VISWAJITH1997/Gesture-Recognition-Using-Machine-Learning/Desgin Sketch/Sample 4/signLan_etch_paste_mask_top_mirror.pdf

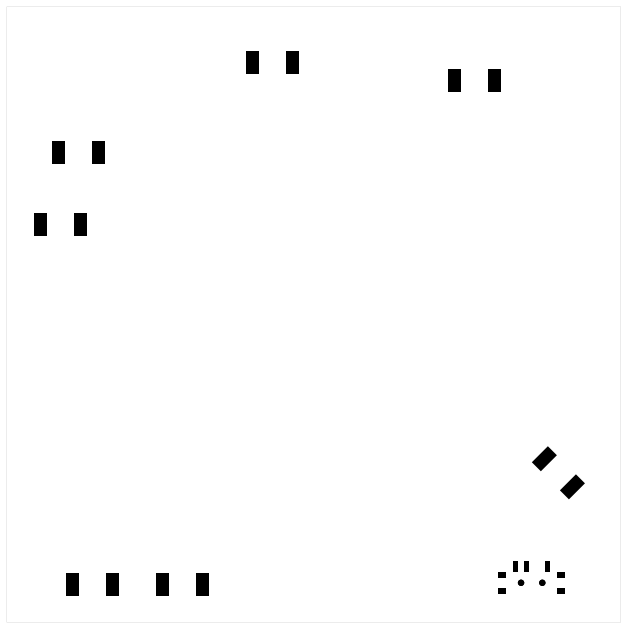
[picture p26: figure]
