VISWAJITH1997/Gesture-Recognition-Using-Machine-Learning/Screenshots/cmd sprint.png

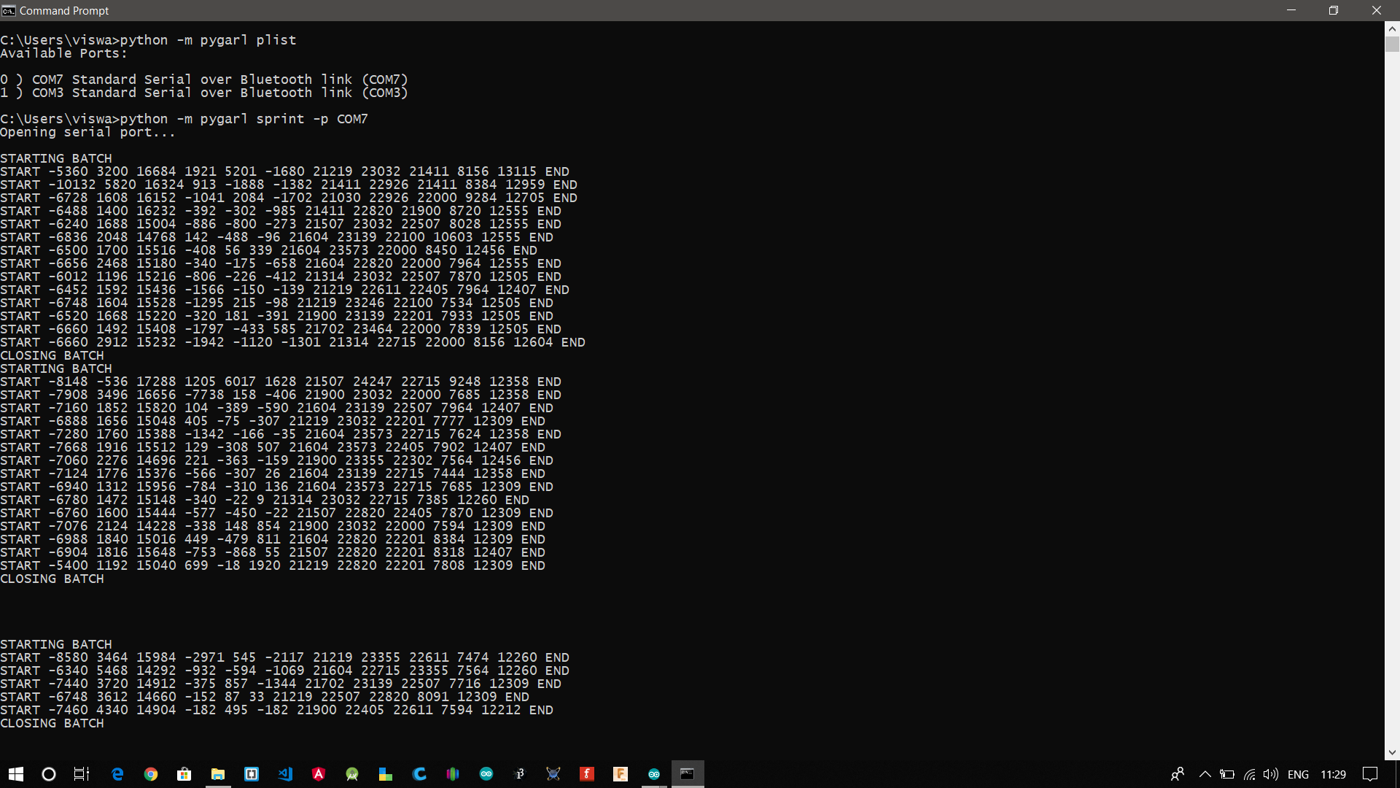
Screenshots/cmd sprint.png
