VISWAJITH1997/Gesture-Recognition-Using-Machine-Learning/Screenshots/Android Serial Print.jpg

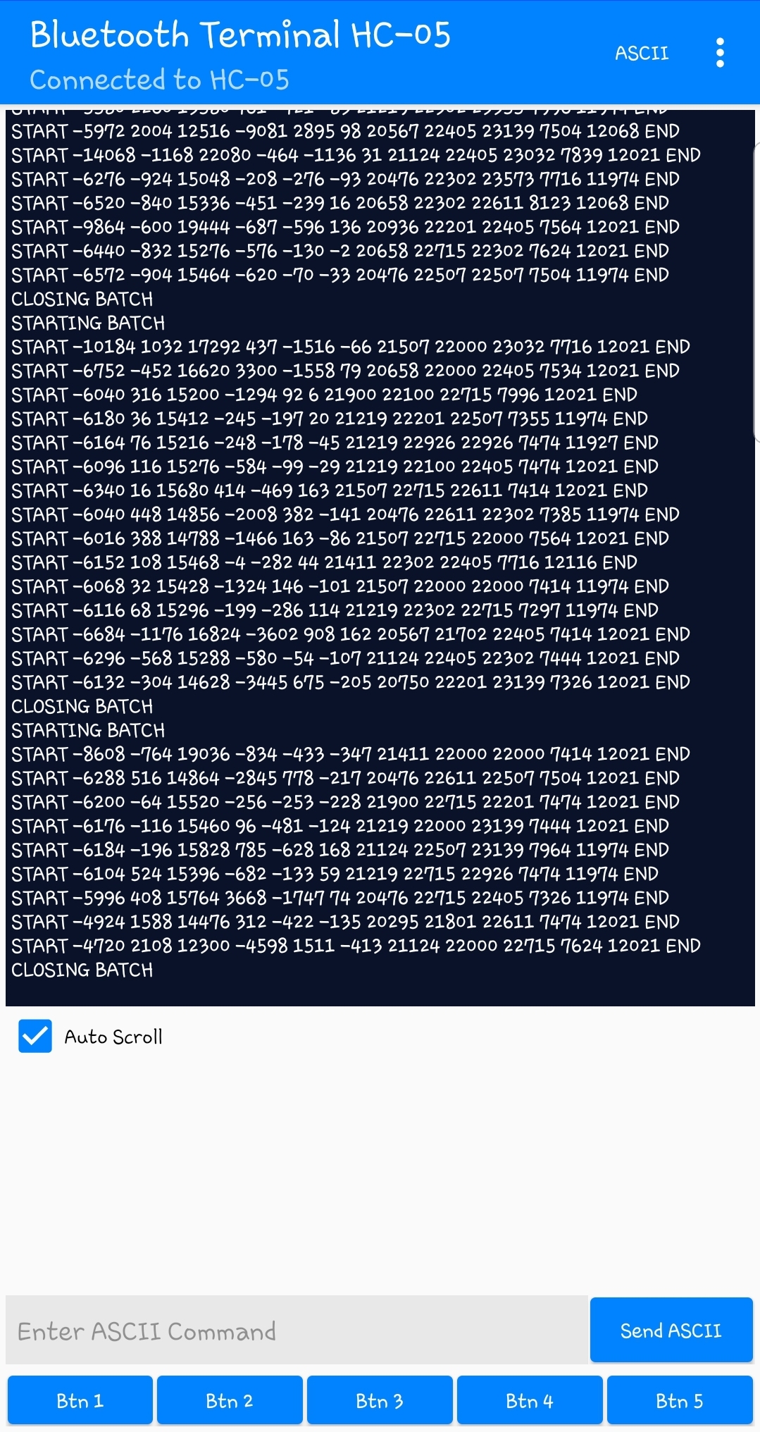
Screenshots/Android Serial Print.jpg
