VISWAJITH1997/Gesture-Recognition-Using-Machine-Learning/Codes/Connections/Untitled Sketch_etch_silk_bottom.pdf

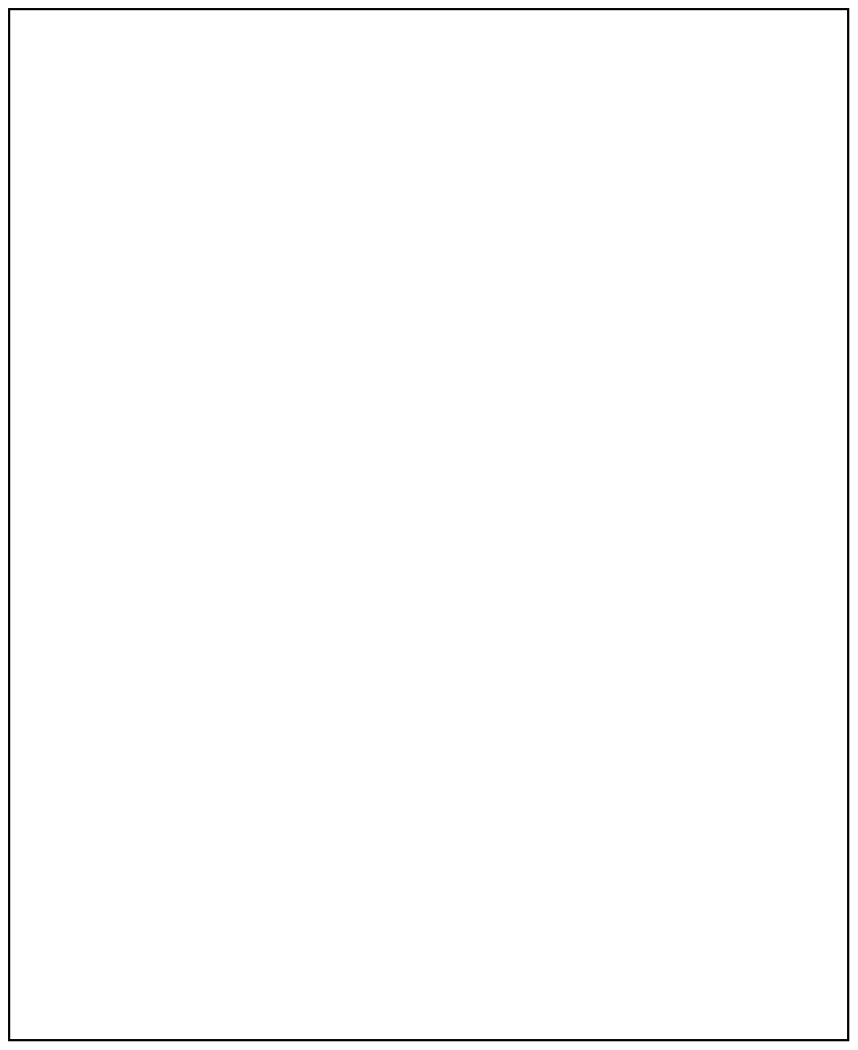
[picture p43: page 1]
