VISWAJITH1997/Gesture-Recognition-Using-Machine-Learning/Codes/Connections/Untitled Sketch_etch_silk_bottom_mirror.pdf

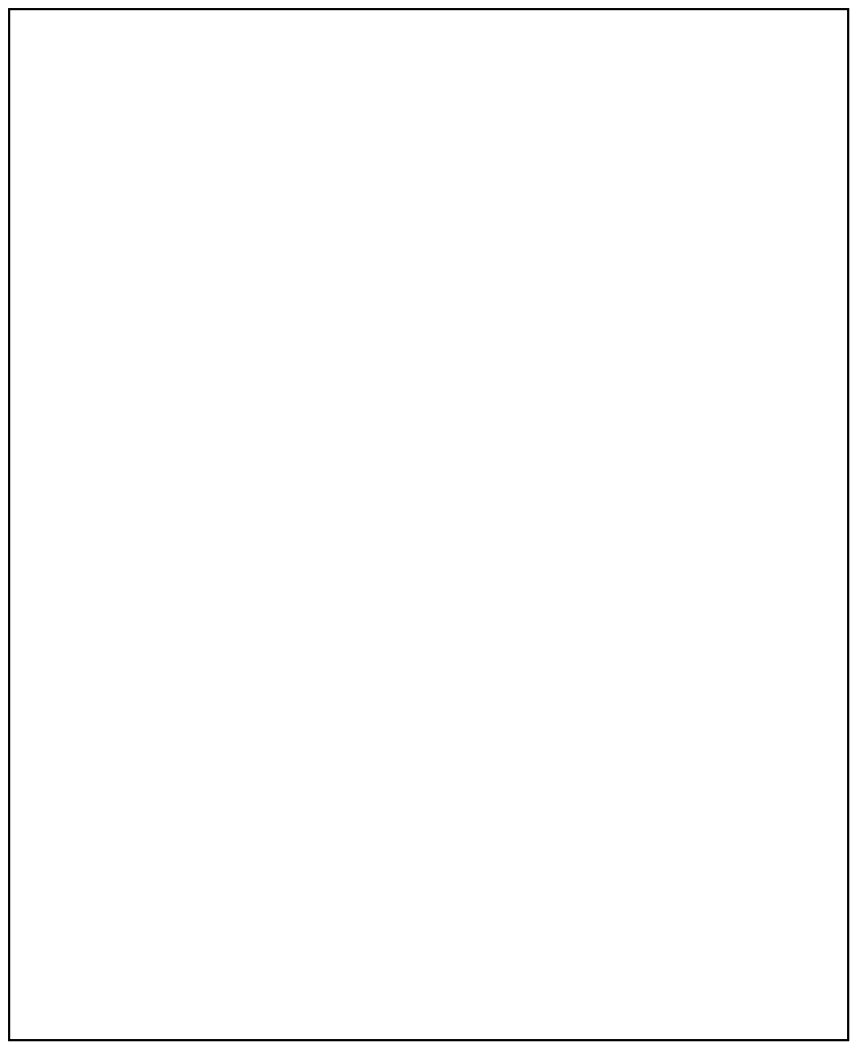
[picture p44: page 1]
