VISWAJITH1997/Gesture-Recognition-Using-Machine-Learning/Codes/Connections/Untitled Sketch_etch_silk_top.pdf

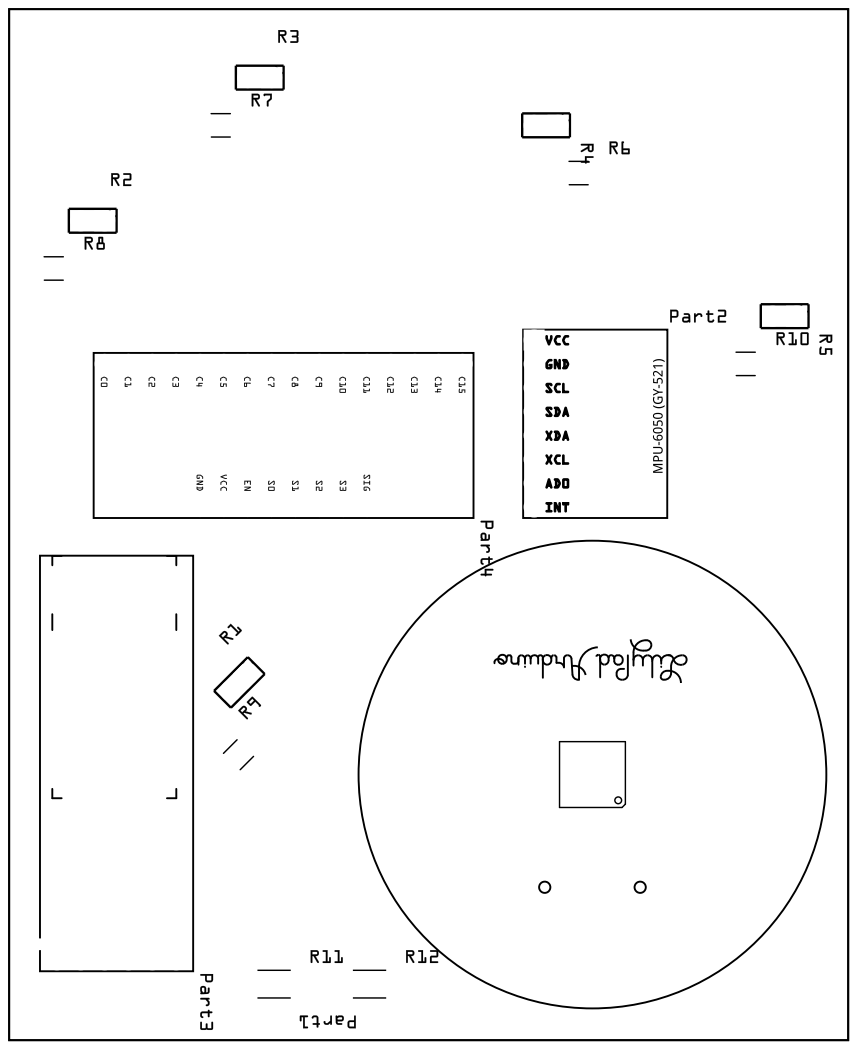
[picture p45: page 1]
