VISWAJITH1997/Gesture-Recognition-Using-Machine-Learning/Codes/Connections/Untitled Sketch_etch_silk_top_mirror.pdf

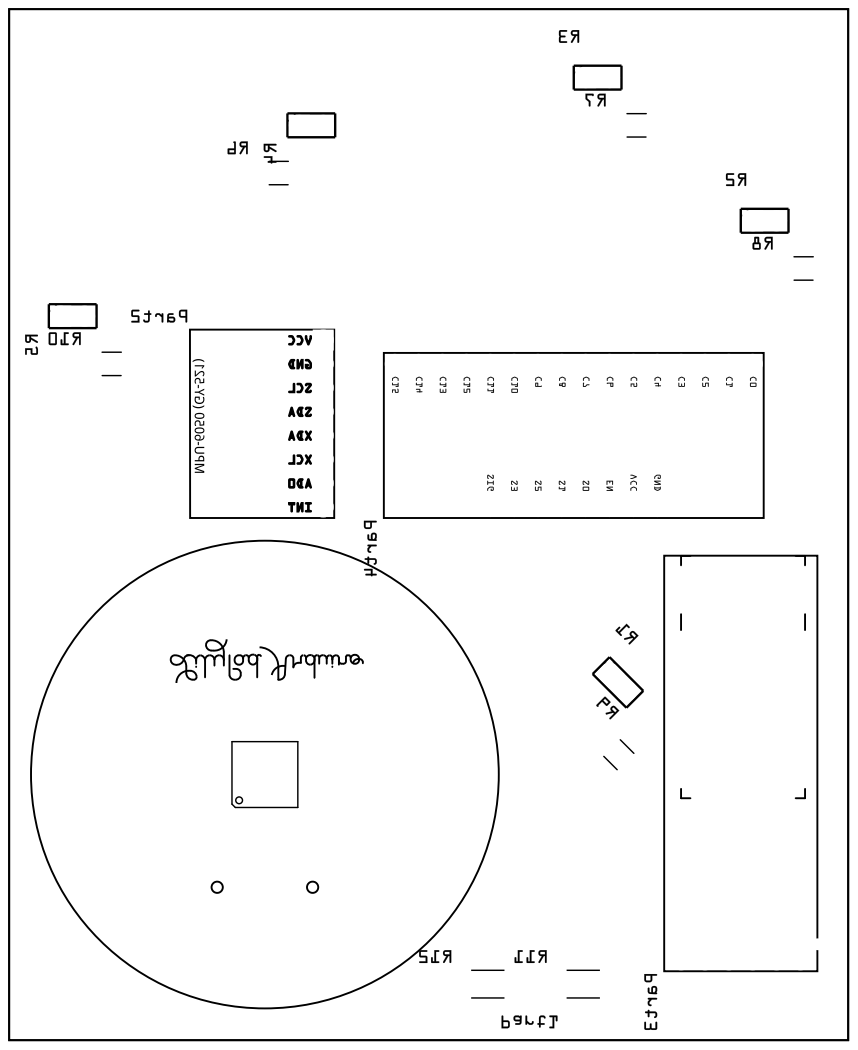
[picture p46: page 1]
