VISWAJITH1997/Gesture-Recognition-Using-Machine-Learning/Desgin Sketch/Sample 2/SignLanguage_etch_copper_bottom.pdf

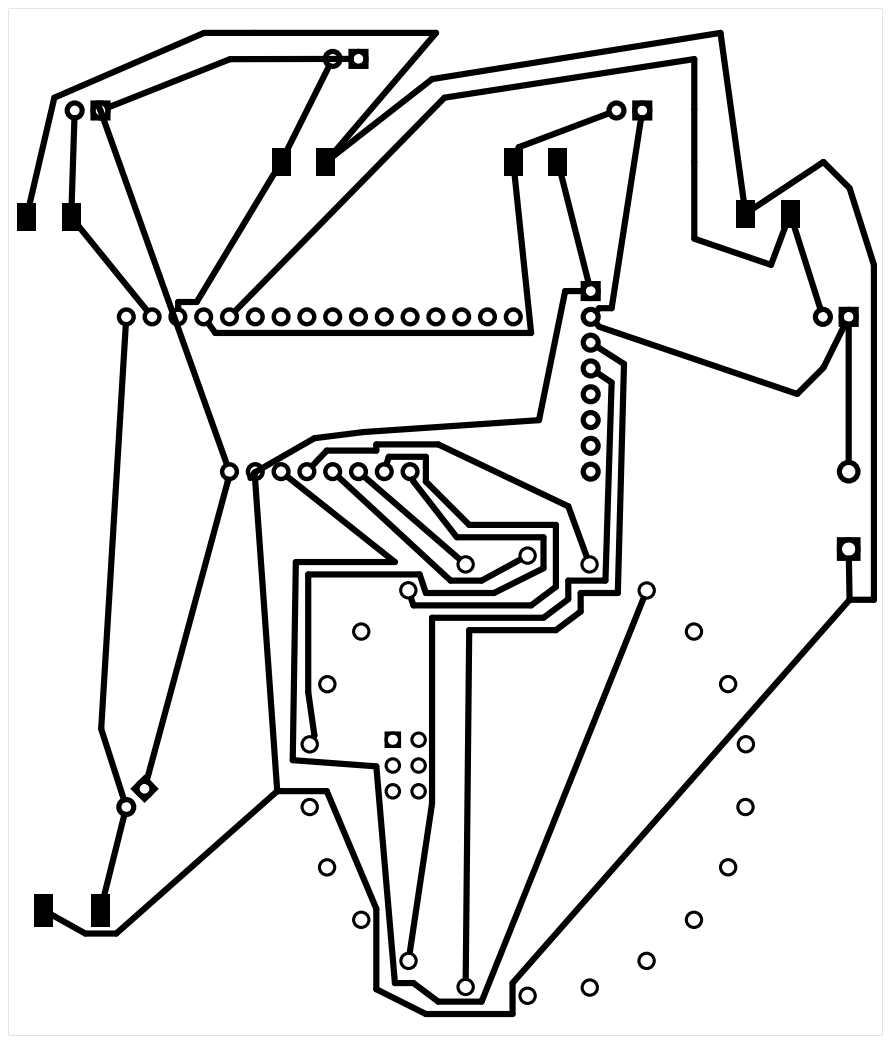
[picture p47: page 1]
