VISWAJITH1997/Gesture-Recognition-Using-Machine-Learning/Desgin Sketch/Sample 2/SignLanguage_etch_copper_bottom_mirror.pdf

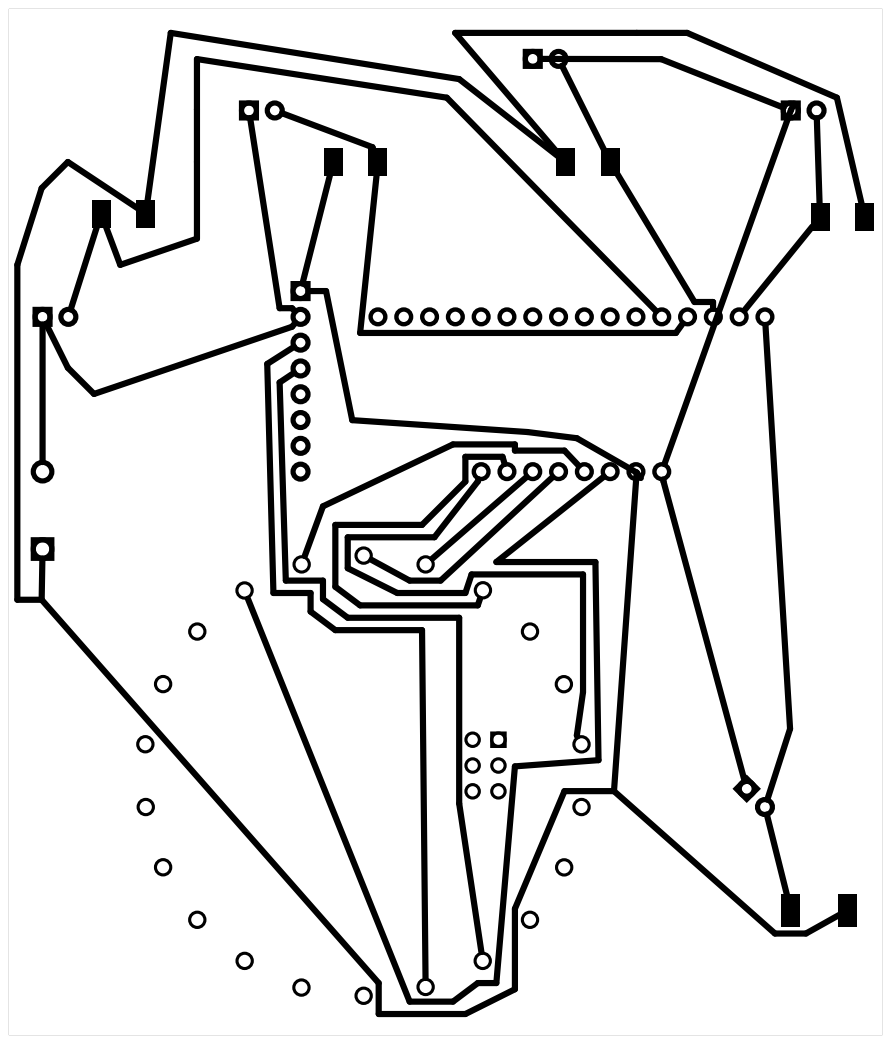
[picture p48: page 1]
