VISWAJITH1997/Gesture-Recognition-Using-Machine-Learning/Desgin Sketch/Sample 2/SignLanguage_etch_copper_top.pdf

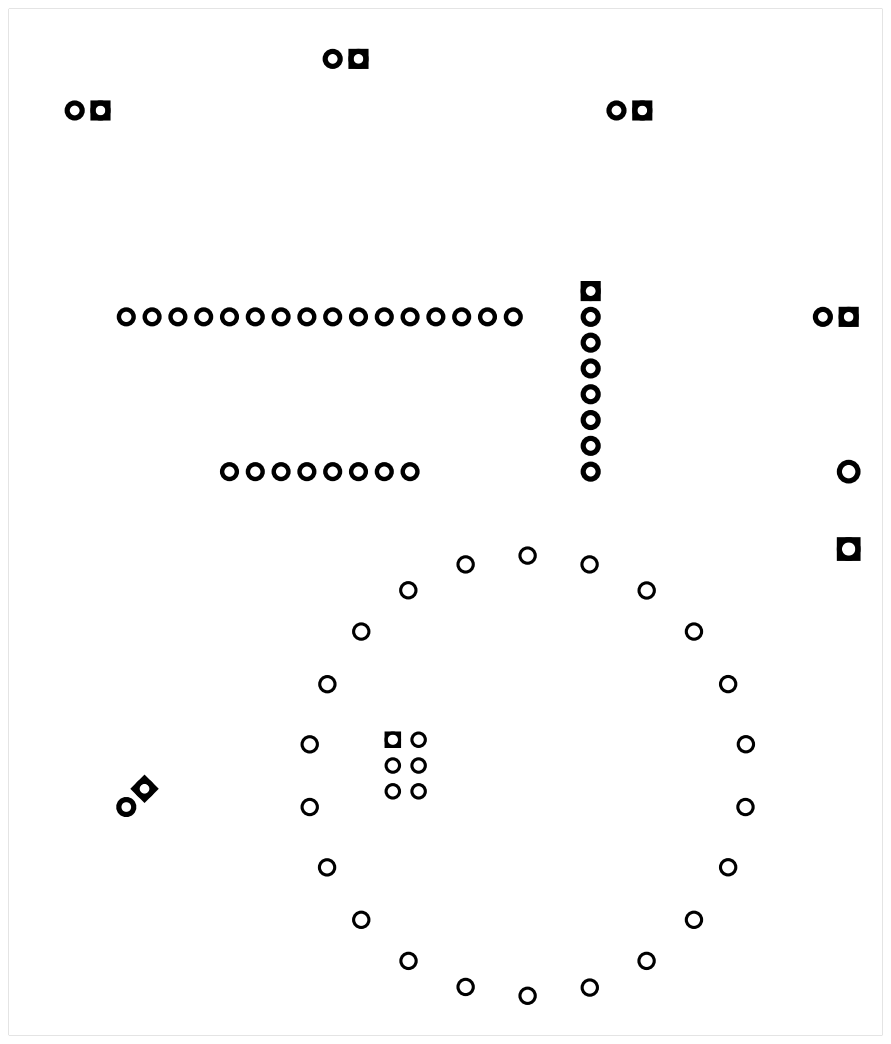
[picture p49: page 1]
