VISWAJITH1997/Gesture-Recognition-Using-Machine-Learning/Desgin Sketch/Sample 2/SignLanguage_etch_copper_top_mirror.pdf

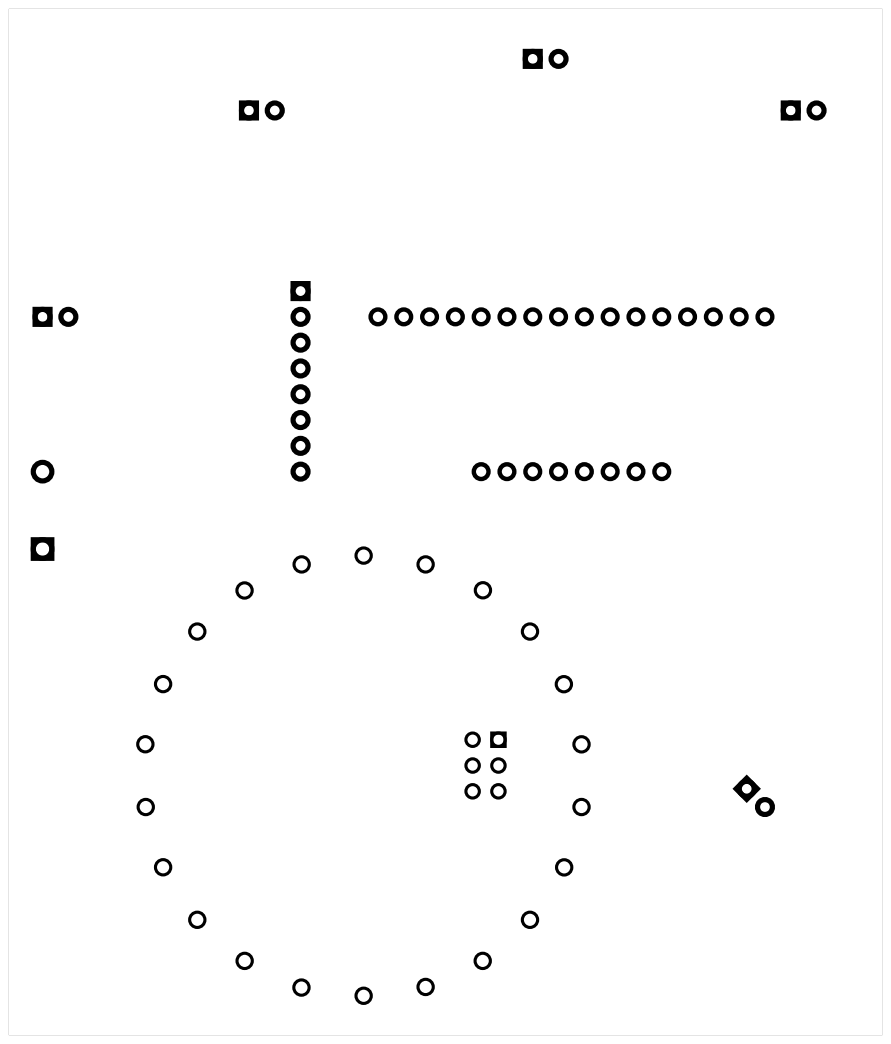
[picture p50: page 1]
