VISWAJITH1997/Gesture-Recognition-Using-Machine-Learning/Desgin Sketch/Sample 2/SignLanguage_etch_mask_bottom.pdf

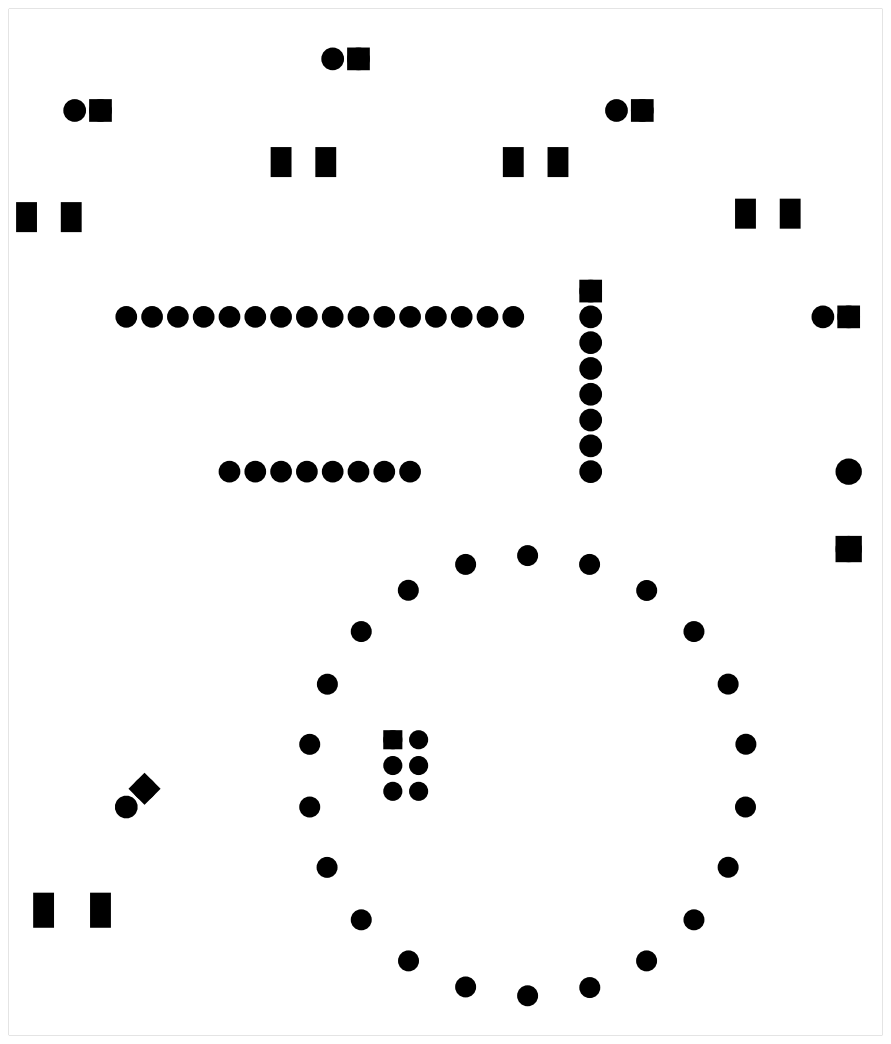
[picture p51: page 1]
