VISWAJITH1997/Gesture-Recognition-Using-Machine-Learning/Desgin Sketch/Sample 2/SignLanguage_etch_mask_bottom_mirror.pdf

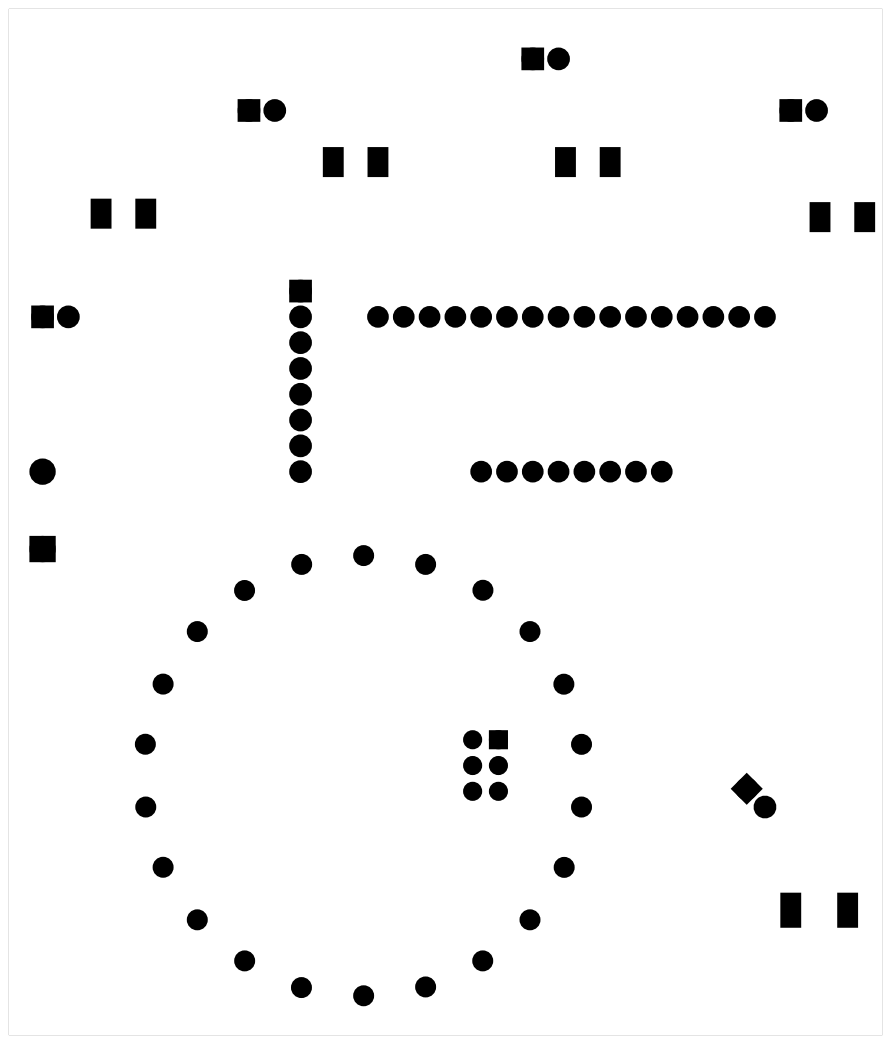
[picture p52: page 1]
