VISWAJITH1997/Gesture-Recognition-Using-Machine-Learning/Desgin Sketch/Sample 2/SignLanguage_etch_mask_top_mirror.pdf

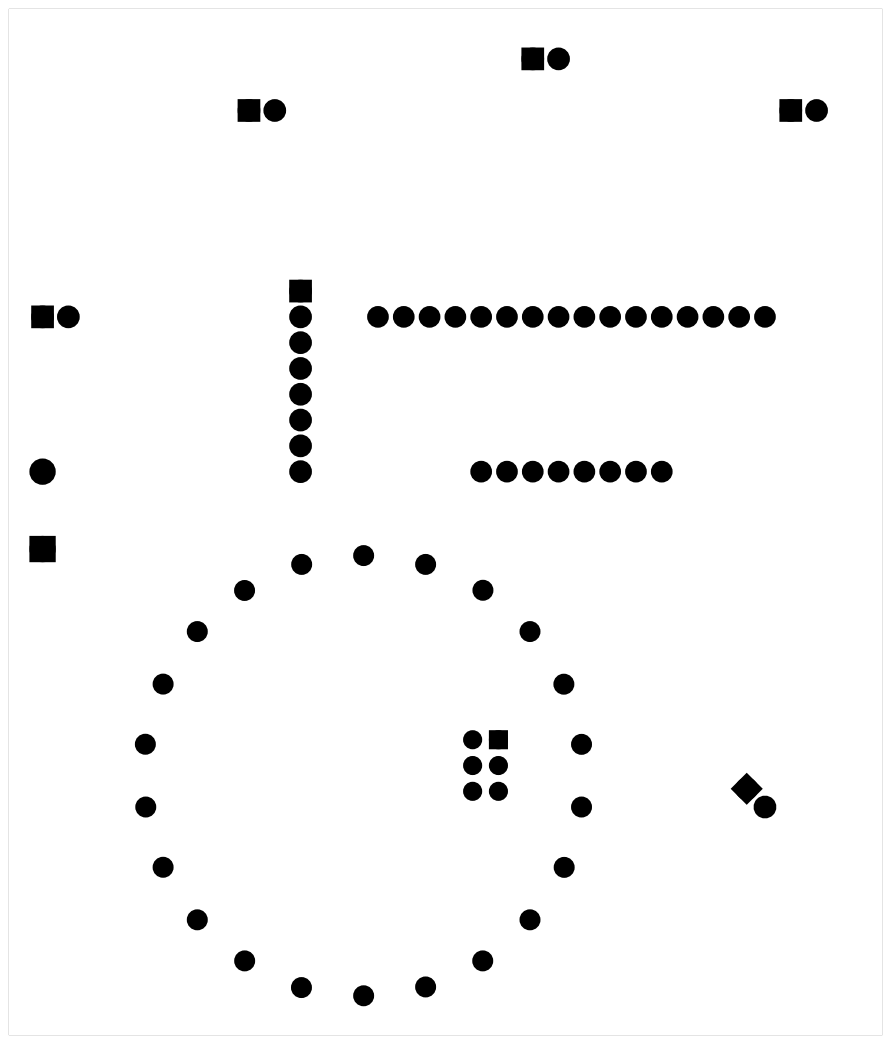
[picture p54: page 1]
