VISWAJITH1997/Gesture-Recognition-Using-Machine-Learning/Desgin Sketch/Sample 2/SignLanguage_etch_silk_bottom_mirror.pdf

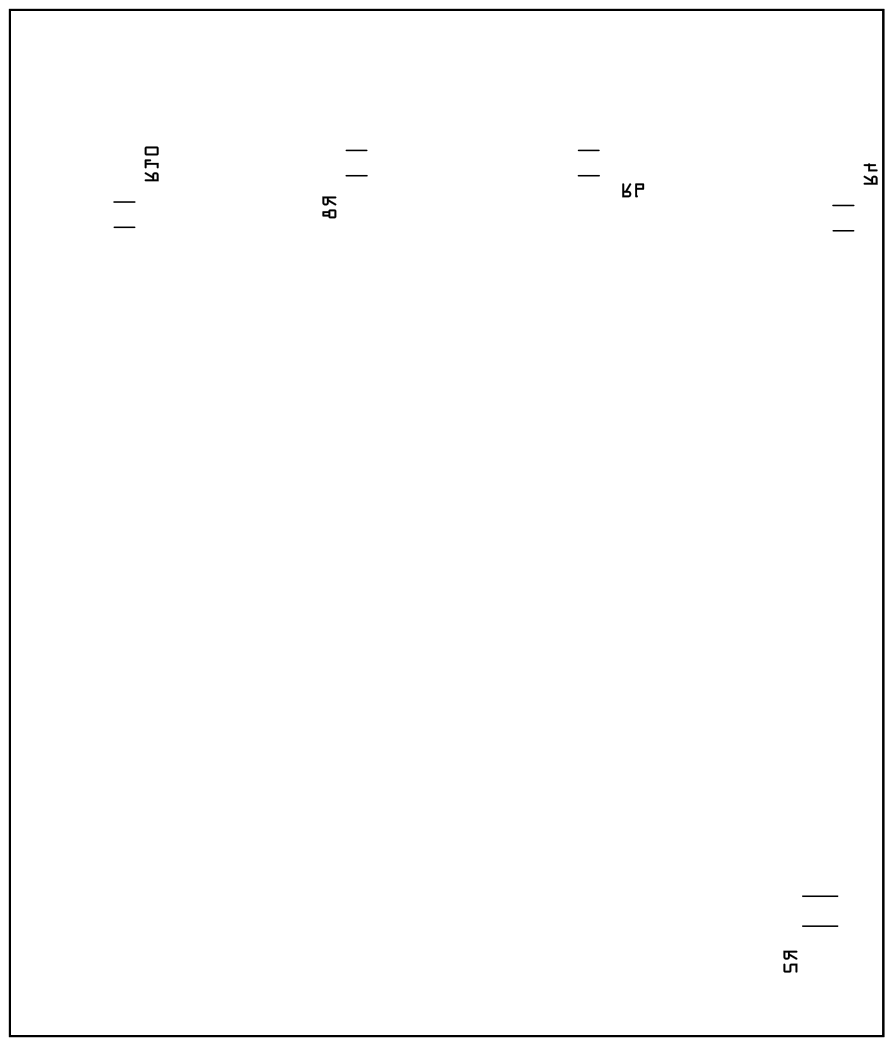
[picture p56: page 1]
