VISWAJITH1997/Gesture-Recognition-Using-Machine-Learning/Desgin Sketch/Sample 2/SignLanguage_etch_silk_top_mirror.pdf

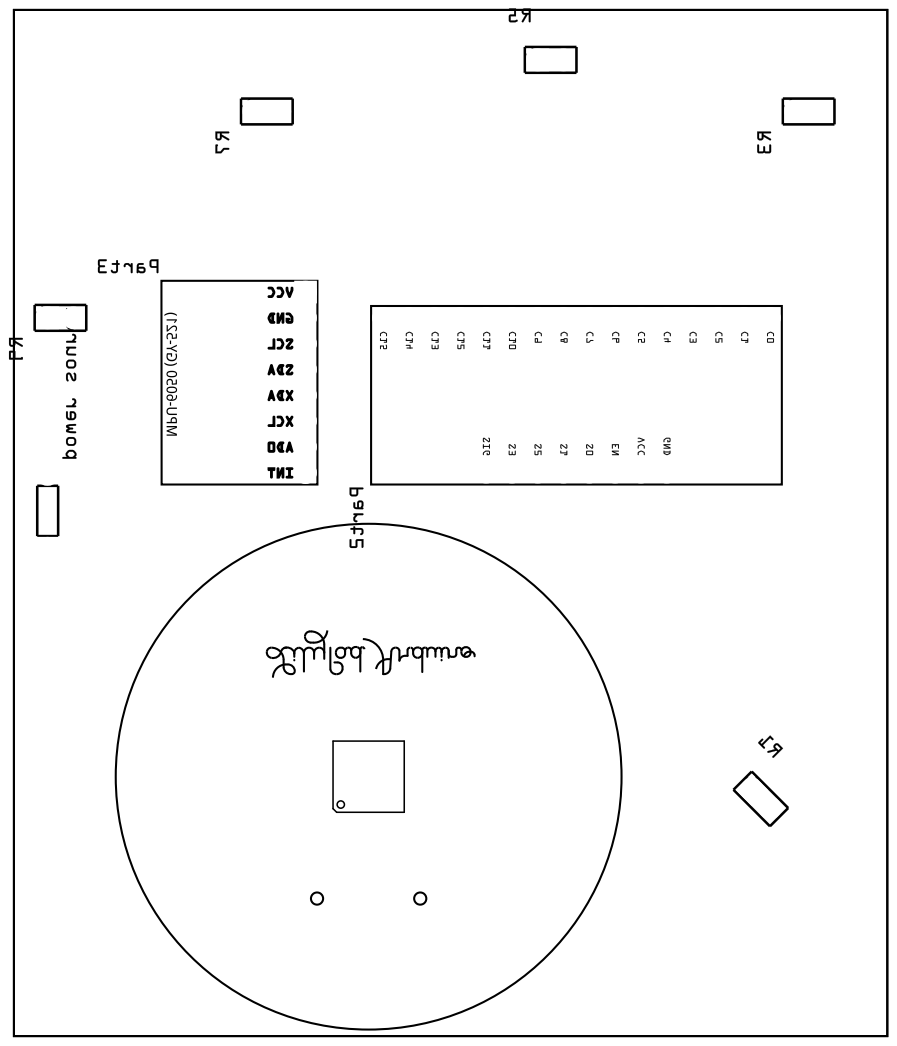
[picture p58: page 1]
