VISWAJITH1997/Gesture-Recognition-Using-Machine-Learning/Desgin Sketch/Sample 3/SignLanguage_etch_copper_bottom.pdf

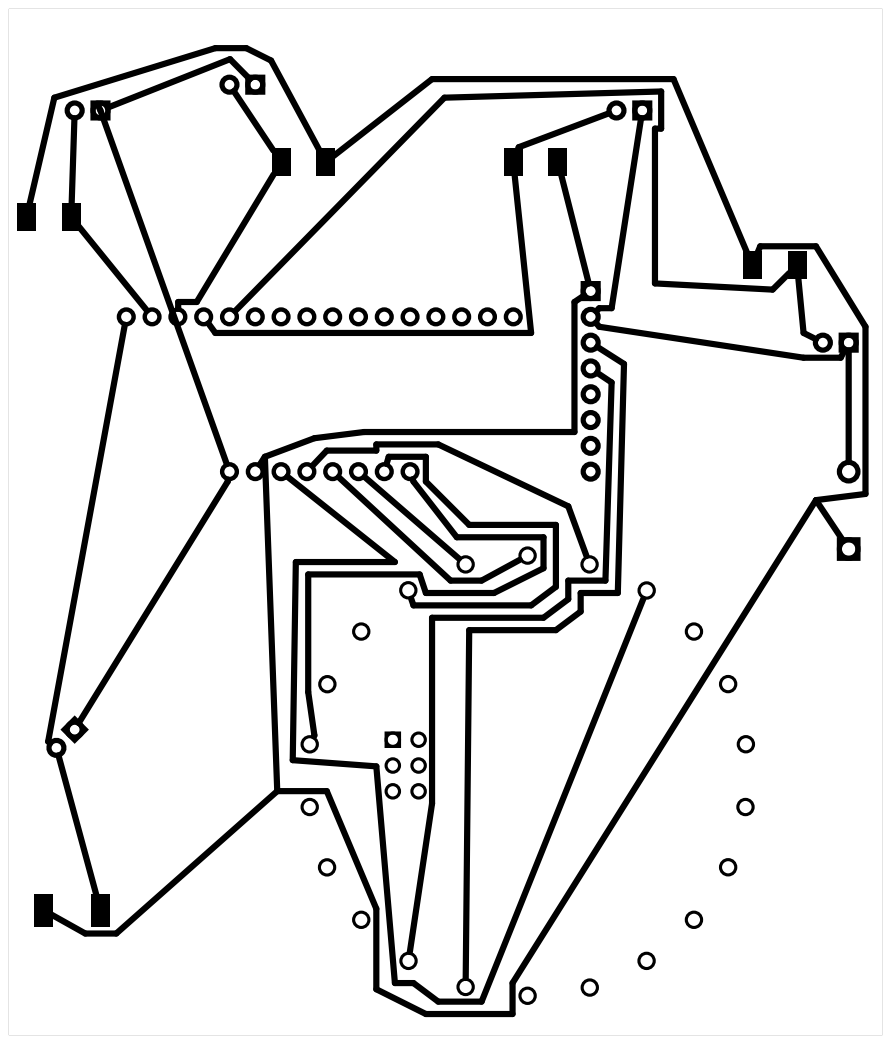
[picture p59: page 1]
