VISWAJITH1997/Gesture-Recognition-Using-Machine-Learning/Desgin Sketch/Sample 3/SignLanguage_etch_copper_bottom_mirror.pdf

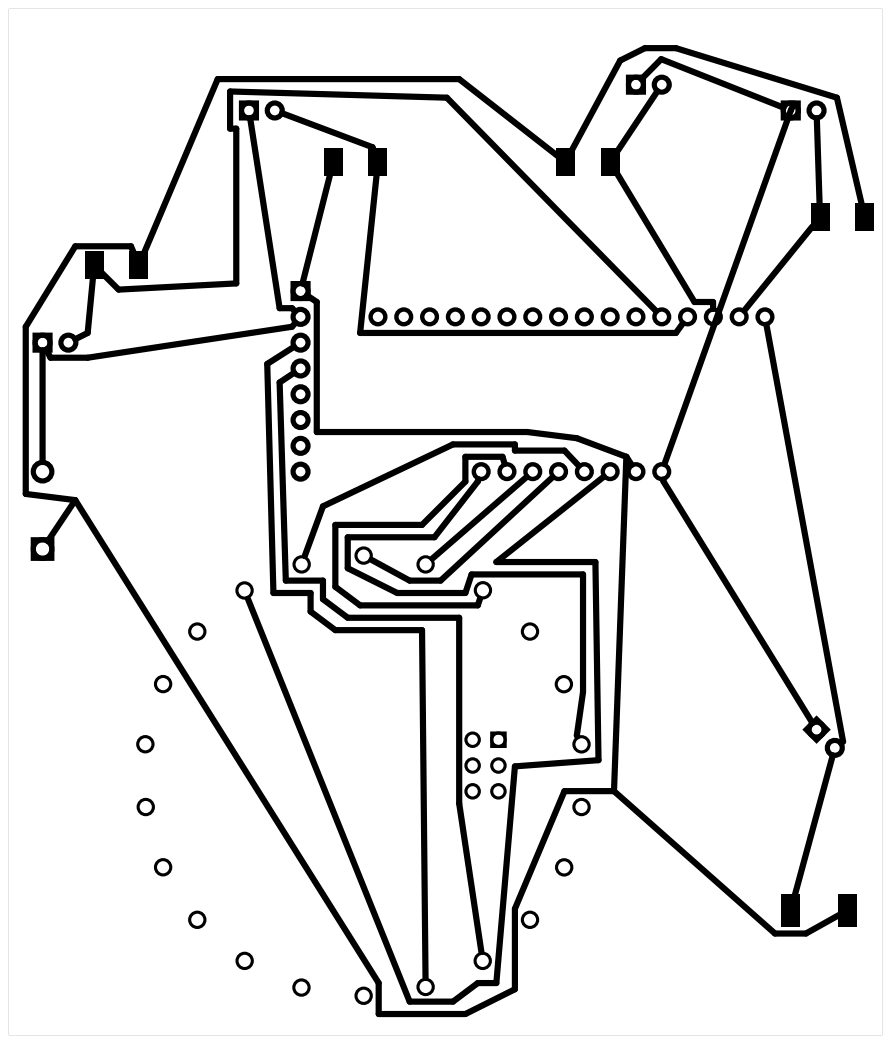
[picture p60: page 1]
