VISWAJITH1997/Gesture-Recognition-Using-Machine-Learning/Desgin Sketch/Sample 3/SignLanguage_etch_mask_bottom.pdf

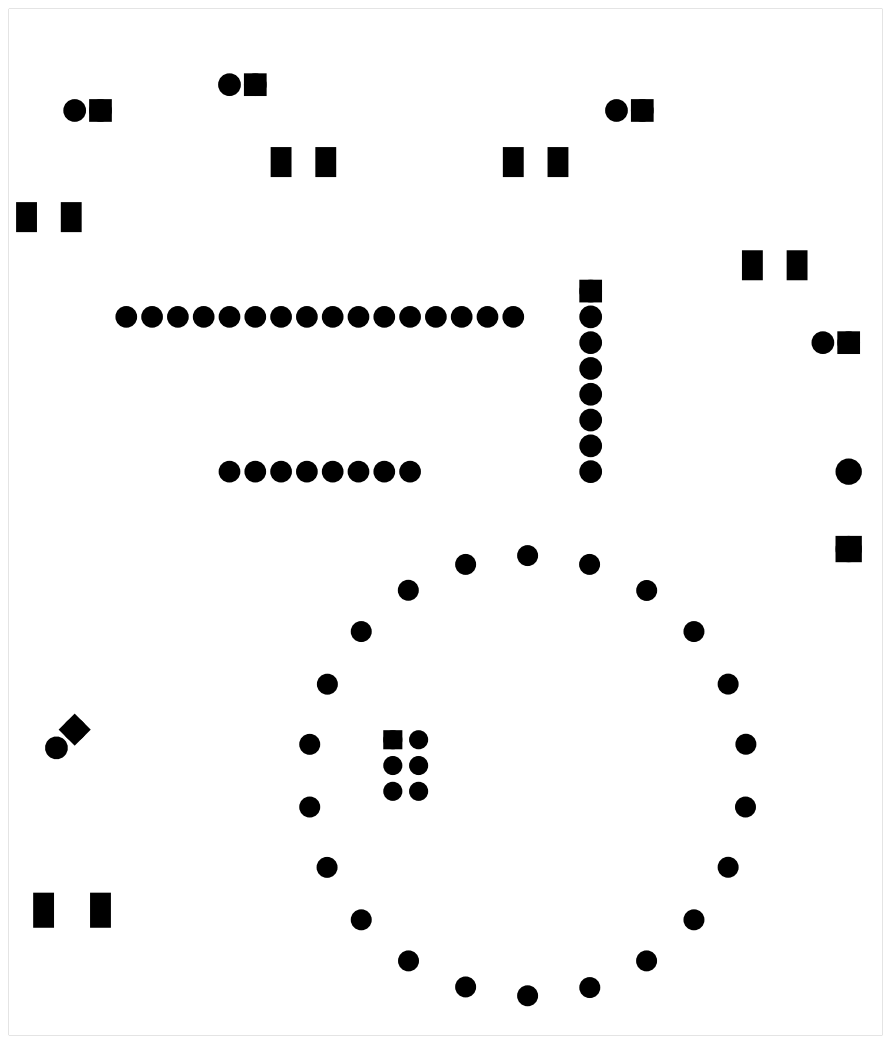
[picture p61: page 1]
