VISWAJITH1997/Gesture-Recognition-Using-Machine-Learning/Desgin Sketch/Sample 3/SignLanguage_etch_mask_bottom_mirror.pdf

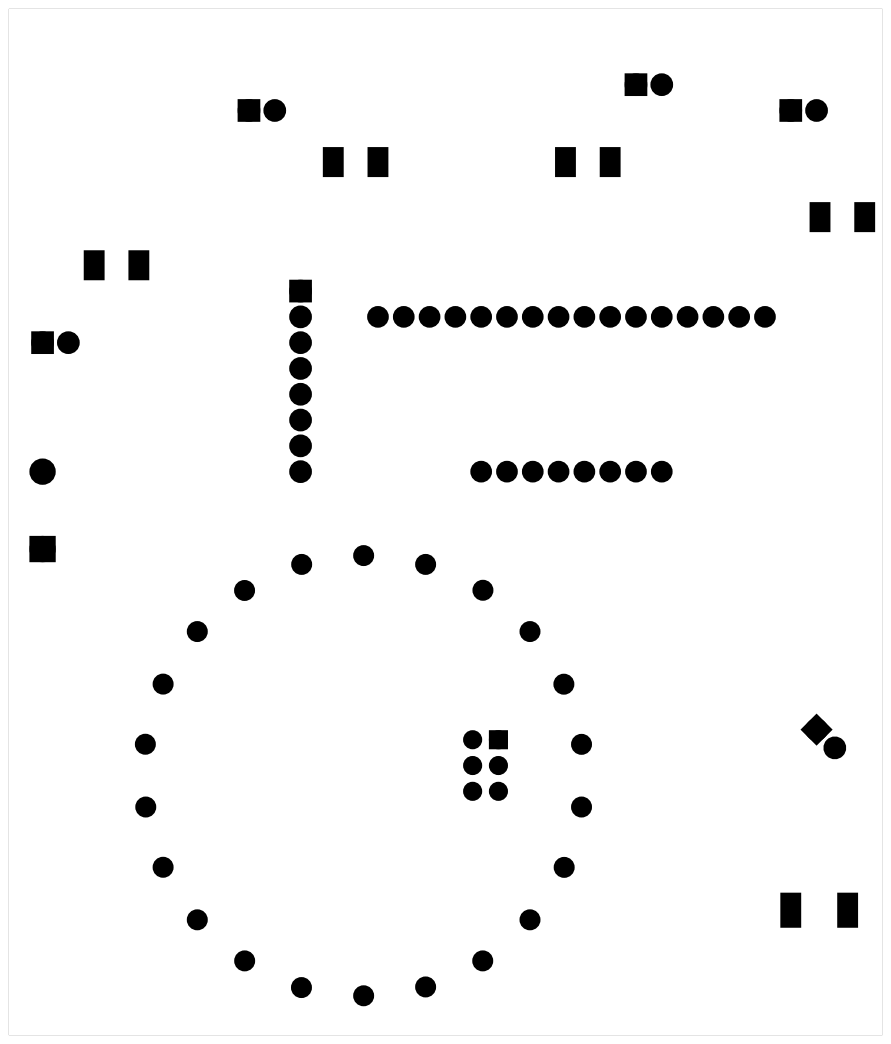
[picture p62: page 1]
