VISWAJITH1997/Gesture-Recognition-Using-Machine-Learning/Desgin Sketch/Sample 3/SignLanguage_etch_silk_bottom.pdf

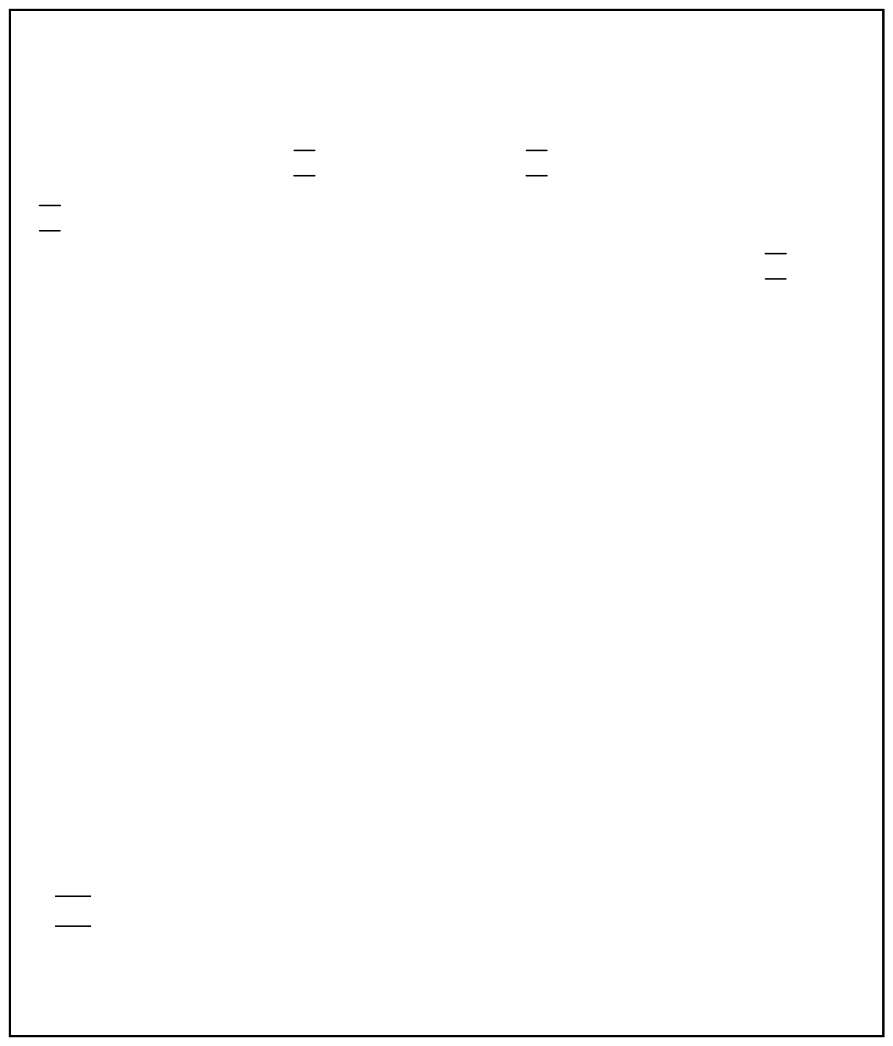
[picture p63: page 1]
