VISWAJITH1997/Gesture-Recognition-Using-Machine-Learning/Desgin Sketch/Sample 3/SignLanguage_etch_silk_bottom_mirror.pdf

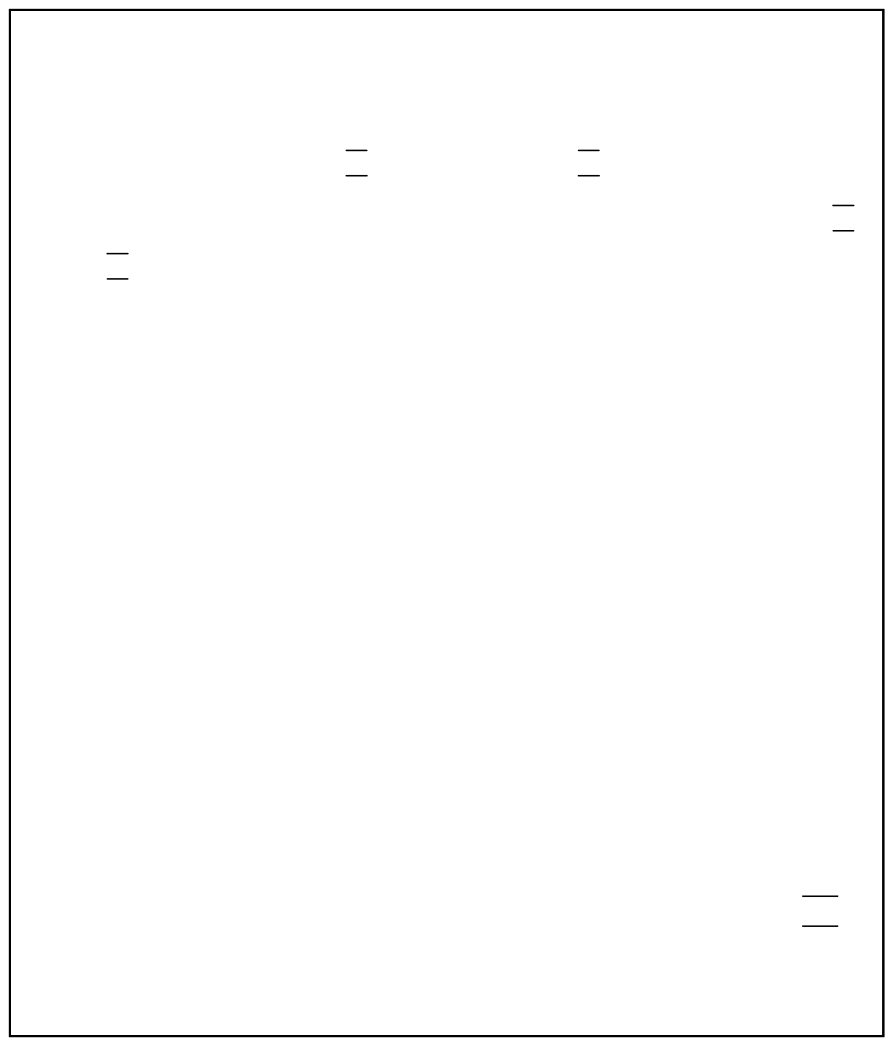
[picture p64: page 1]
