VISWAJITH1997/Gesture-Recognition-Using-Machine-Learning/Desgin Sketch/Sample 4/signLan_etch_copper_bottom.pdf

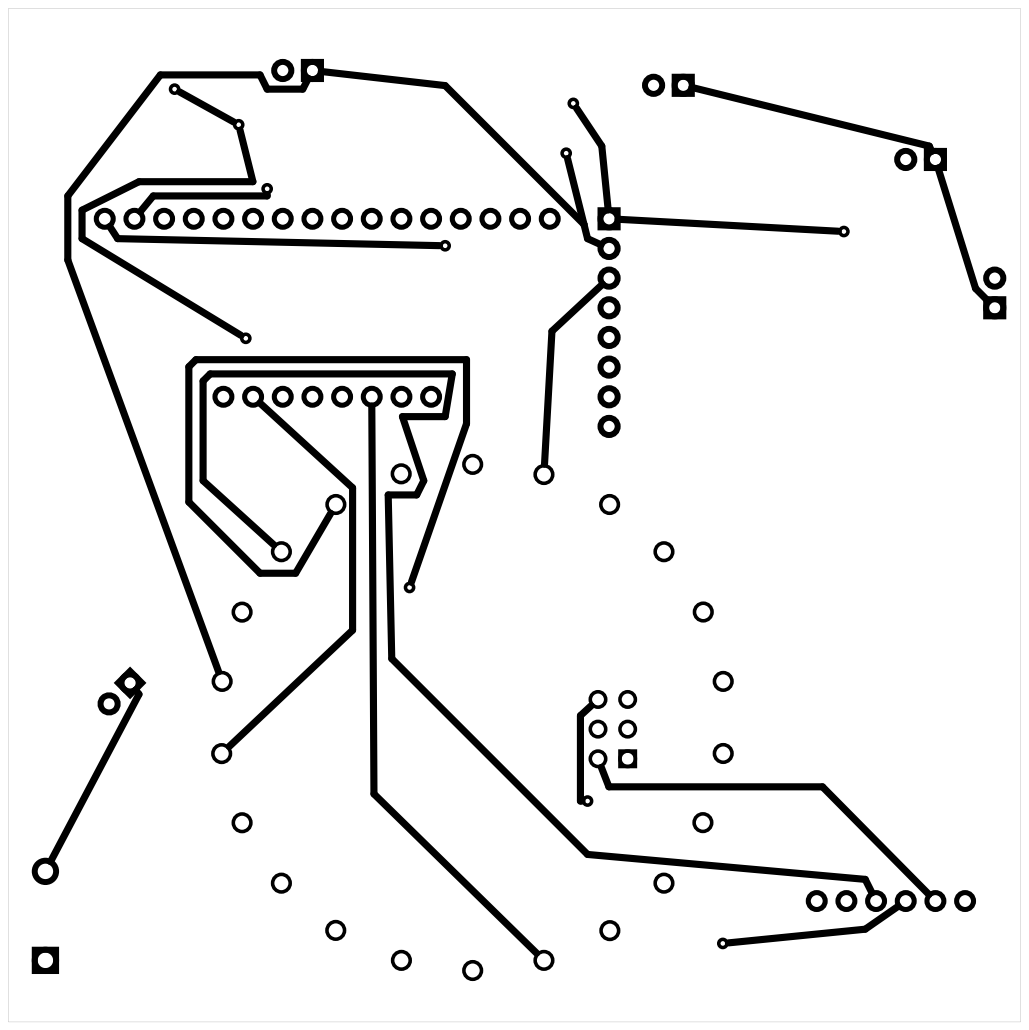
[picture p65: page 1]
