VISWAJITH1997/Gesture-Recognition-Using-Machine-Learning/Desgin Sketch/Sample 4/signLan_etch_copper_bottom_mirror.pdf

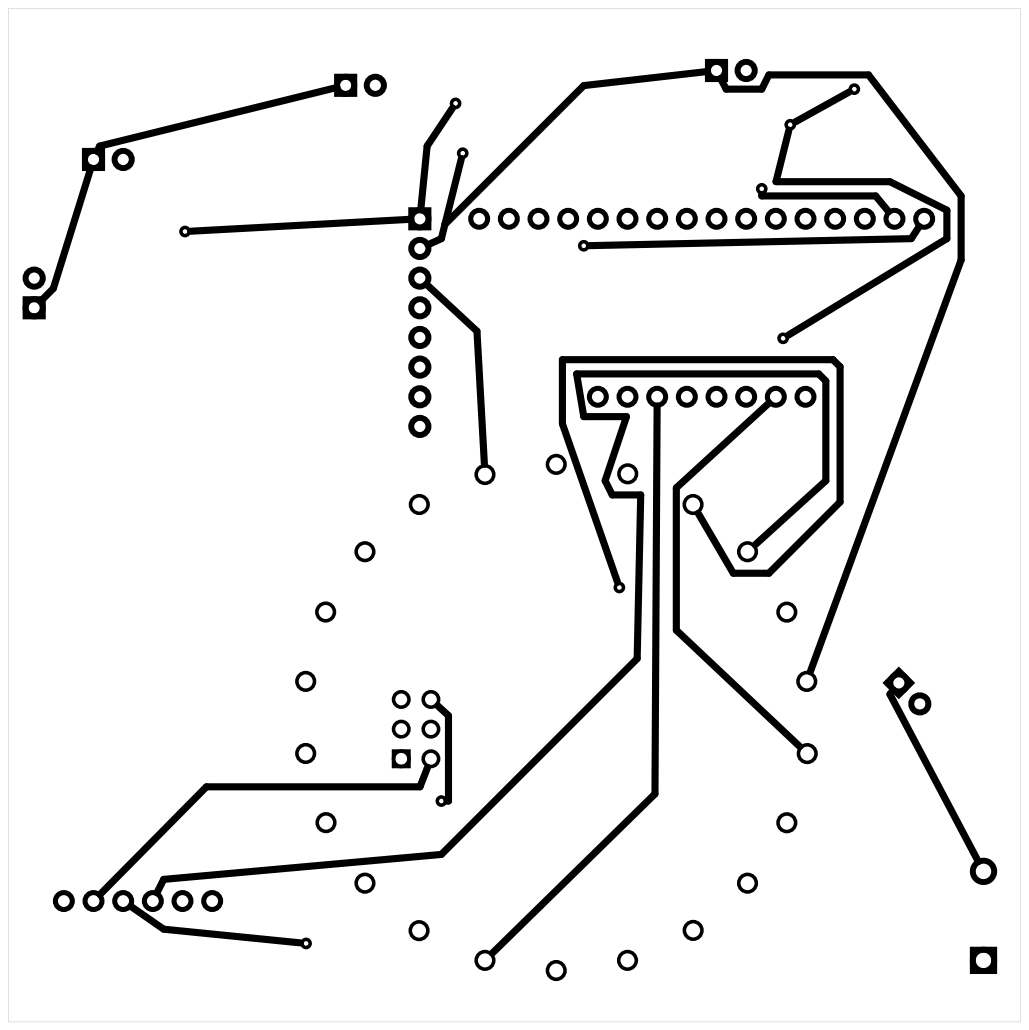
[picture p66: page 1]
