VISWAJITH1997/Gesture-Recognition-Using-Machine-Learning/Desgin Sketch/Sample 4/signLan_etch_copper_top.pdf

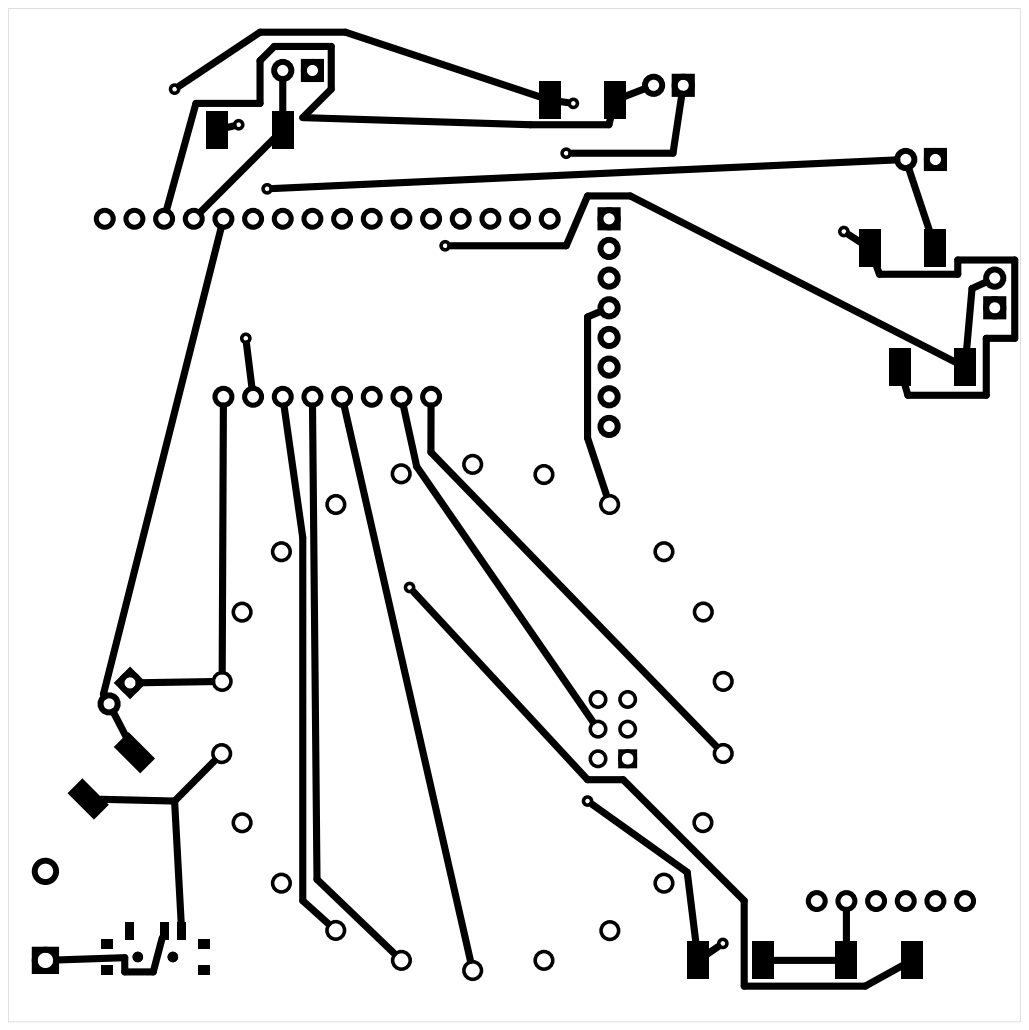
[picture p67: page 1]
