VISWAJITH1997/Gesture-Recognition-Using-Machine-Learning/Desgin Sketch/Sample 4/signLan_etch_copper_top_mirror.pdf

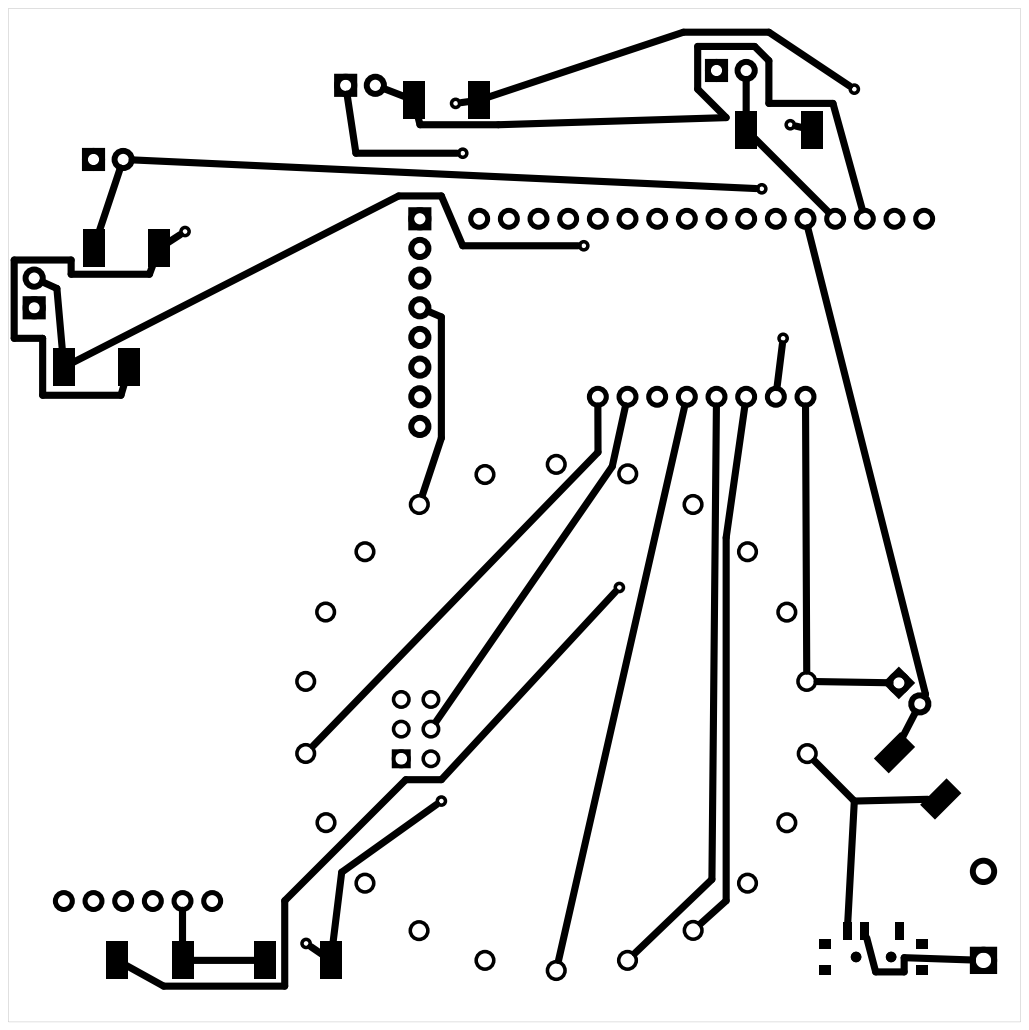
[picture p68: page 1]
