VISWAJITH1997/Gesture-Recognition-Using-Machine-Learning/Desgin Sketch/Sample 4/signLan_etch_mask_bottom_mirror.pdf

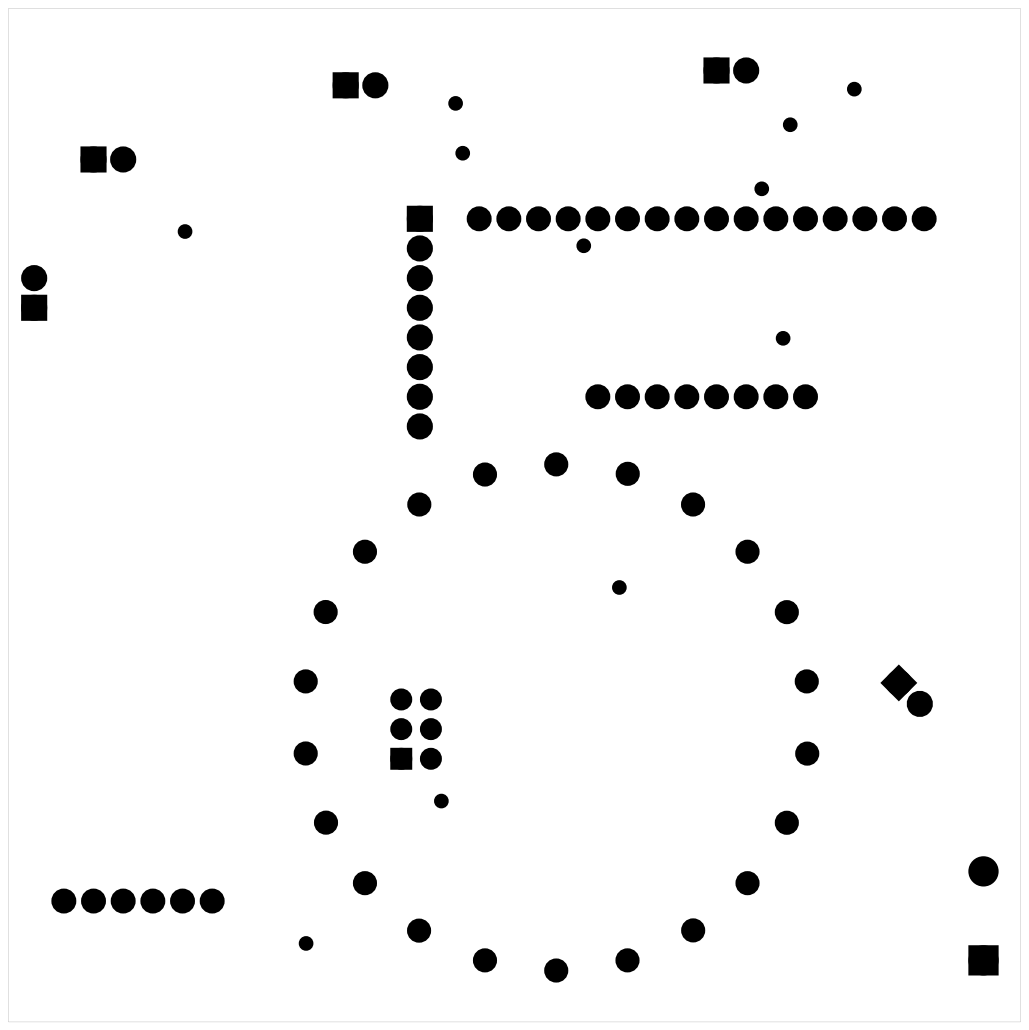
[picture p70: page 1]
