VISWAJITH1997/Gesture-Recognition-Using-Machine-Learning/Desgin Sketch/Sample 4/signLan_etch_mask_top_mirror.pdf

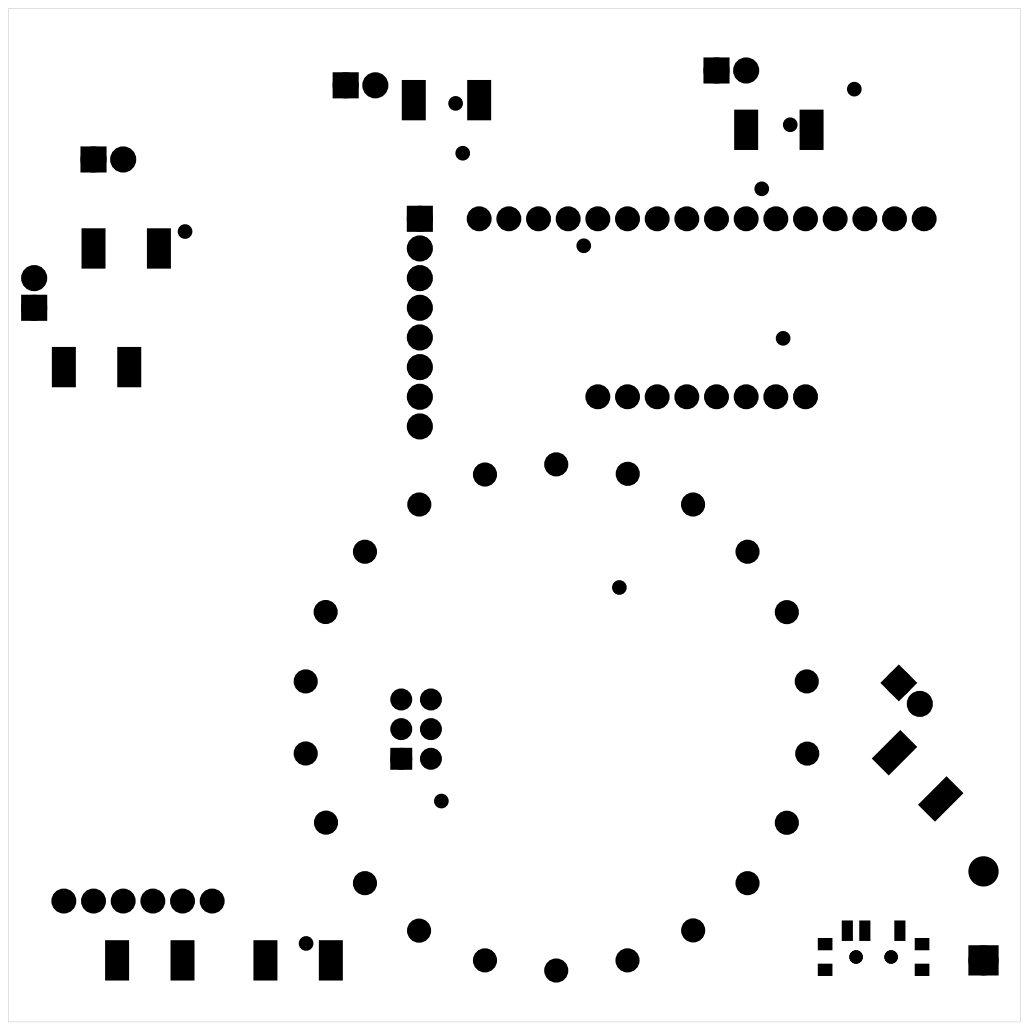
[picture p72: page 1]
