VISWAJITH1997/Gesture-Recognition-Using-Machine-Learning/Desgin Sketch/Sample 4/signLan_etch_silk_bottom_mirror.pdf

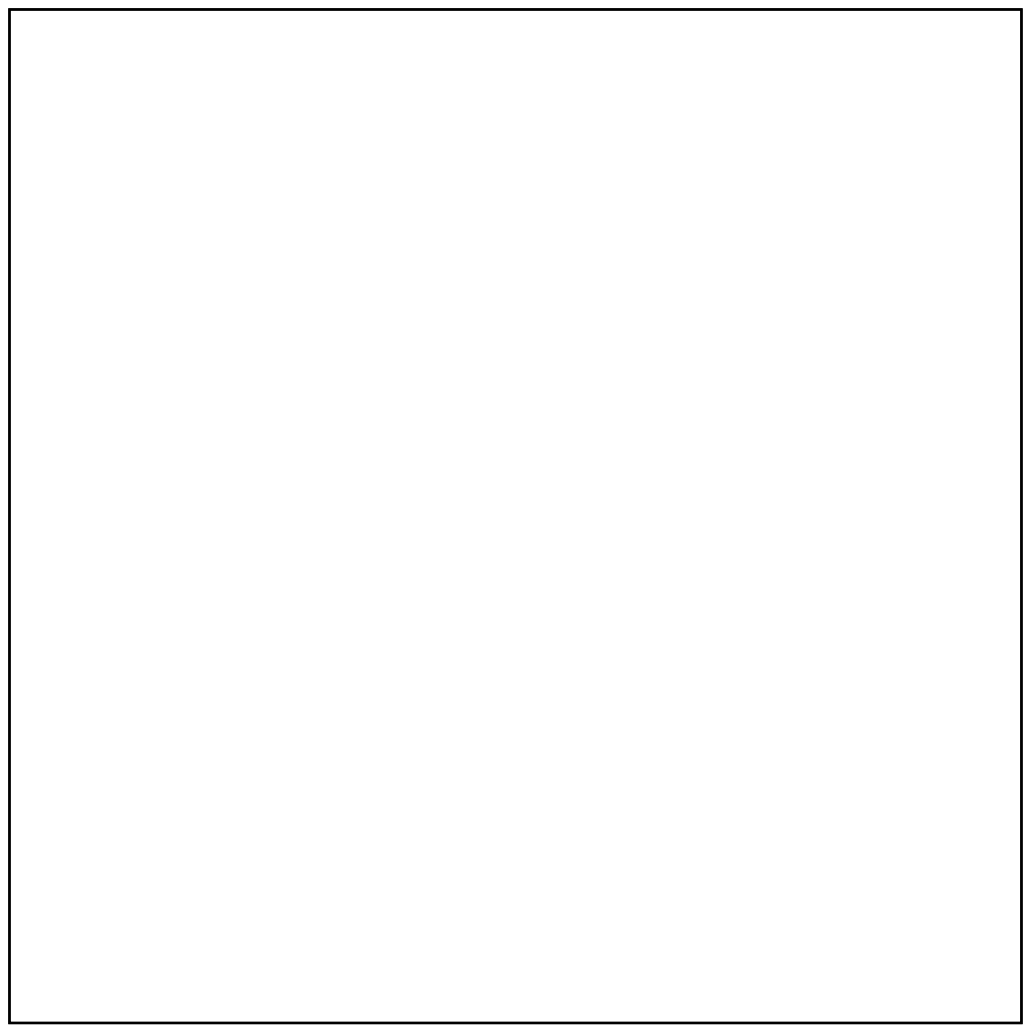
[picture p74: page 1]
