VISWAJITH1997/Gesture-Recognition-Using-Machine-Learning/Desgin Sketch/Sample 4/signLan_etch_silk_top_mirror.pdf

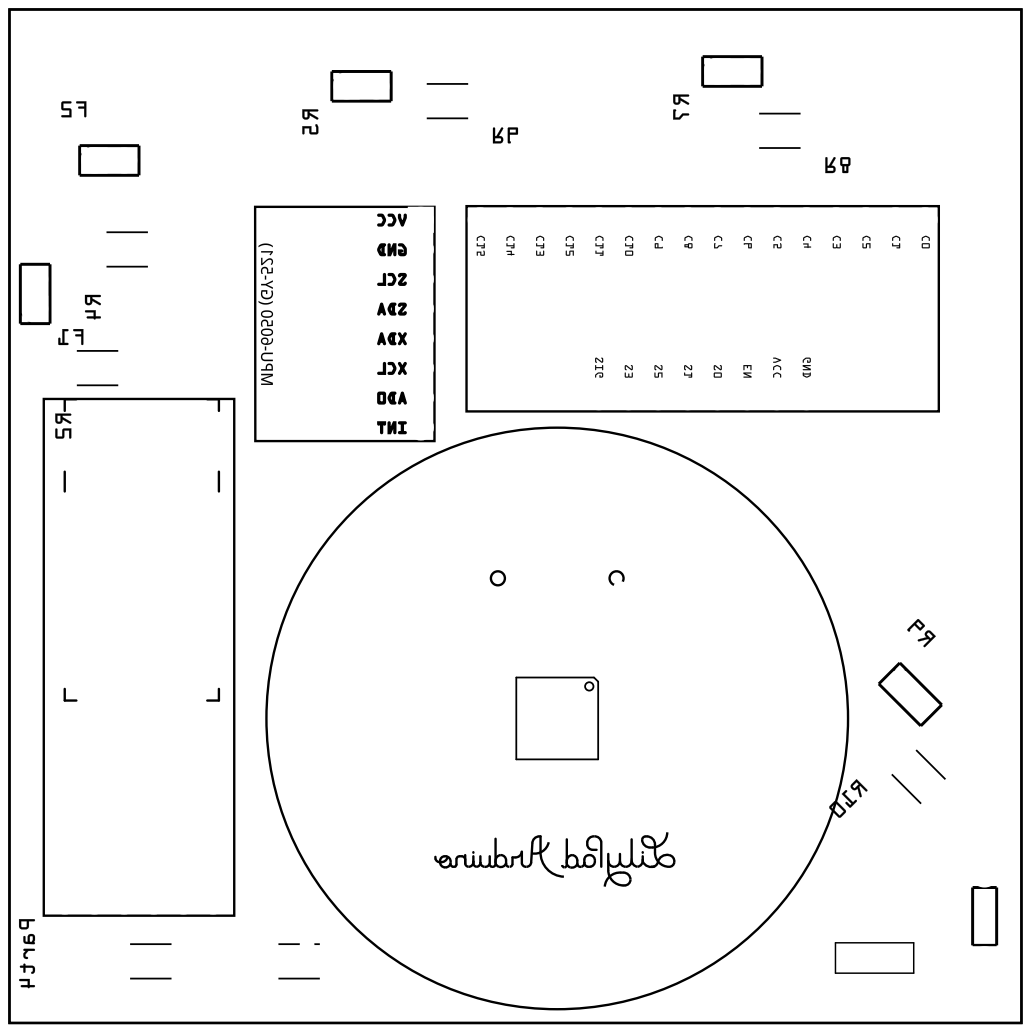
[picture p76: page 1]
